geg-tech/biblicallyaccuratekeyboard/CAD/Keycaps/eyecap 2-wide.step

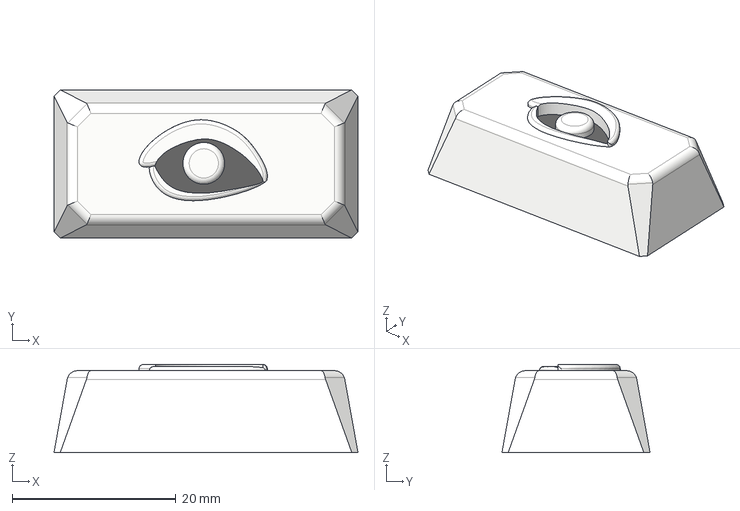
[picture p18: CAD file, 2025-06-16]
CAD/Keycaps/eyecap 2-wide.step
37.2 x 18.1 x 10.8 mm
