geg-tech/biblicallyaccuratekeyboard/CAD/Sections/inner ring opening section.step

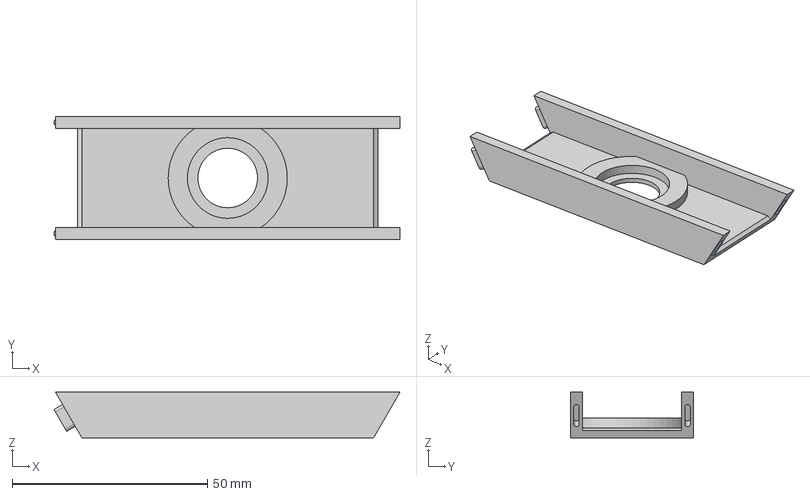
[picture p19: CAD file, 2025-06-16]
CAD/Sections/inner ring opening section.step
88.5 x 31.5 x 11.7 mm
