geg-tech/biblicallyaccuratekeyboard/CAD/Keycaps/eyecap 3-wide sclera.step

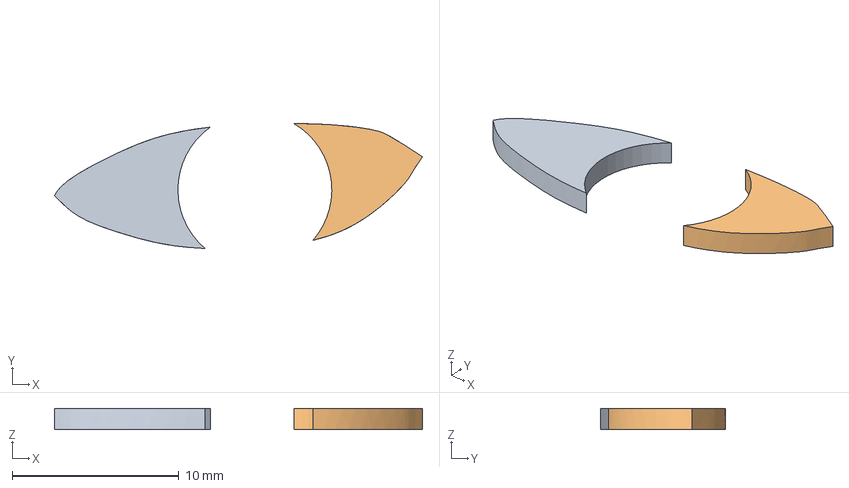
[picture p20: CAD file, 2025-06-16]
CAD/Keycaps/eyecap 3-wide sclera.step
22.1 x 7.51 x 1.27 mm
