geg-tech/biblicallyaccuratekeyboard/CAD/Sections/outer ring section.step

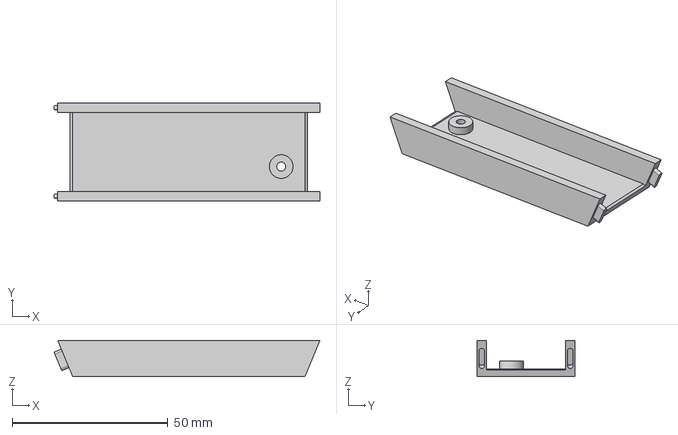
[picture p21: CAD file, 2025-06-16]
CAD/Sections/outer ring section.step
85.5 x 31.5 x 11.7 mm
