geg-tech/biblicallyaccuratekeyboard/CAD/Sections/outer ring opening plate.step

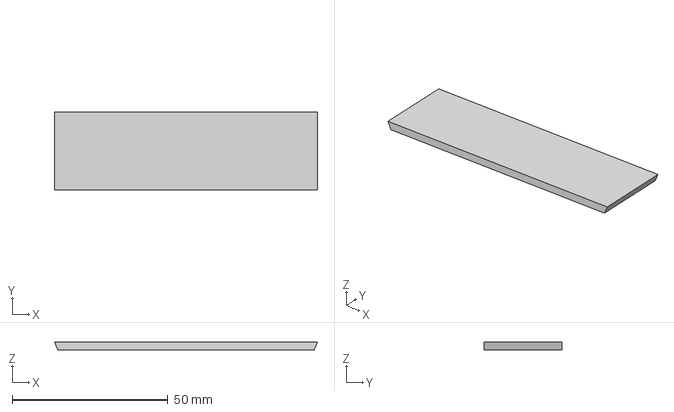
[picture p22: CAD file, 2025-06-16]
CAD/Sections/outer ring opening plate.step
84.4 x 25.0 x 2.54 mm
